dmaone/CSI/MagValve/Cortron_80-551101_rev_D.JPG

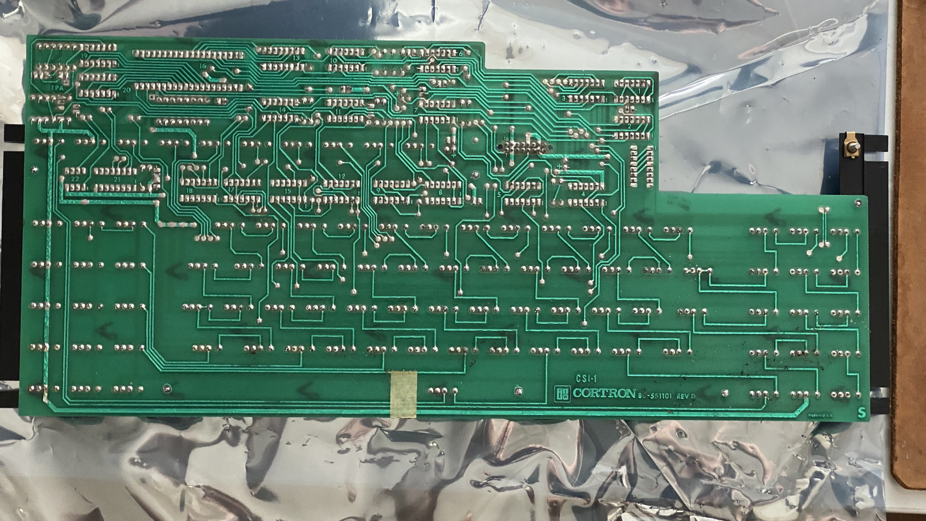
MagValve/Cortron_80-551101_rev_D.JPG
