dmaone/CSI/MagValve/Waveforms/Cortron/Oscillograms/Agilent diffprobe/Screen_2019-10-03000012.png

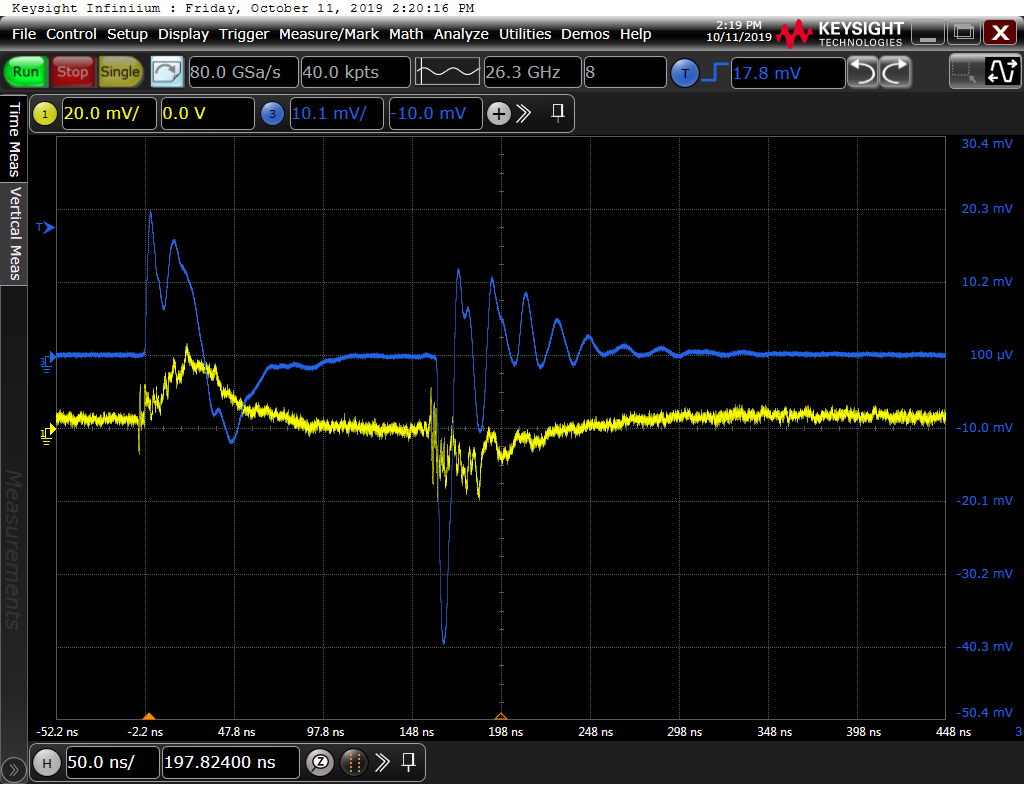
MagValve/Waveforms/Cortron/Oscillograms/Agilent diffprobe/Screen_2019-10-03000012.png
