dmaone/CSI/MagValve/Waveforms/Cortron/Oscillograms/ctrlr-side_ground_bounce/Tek000.png

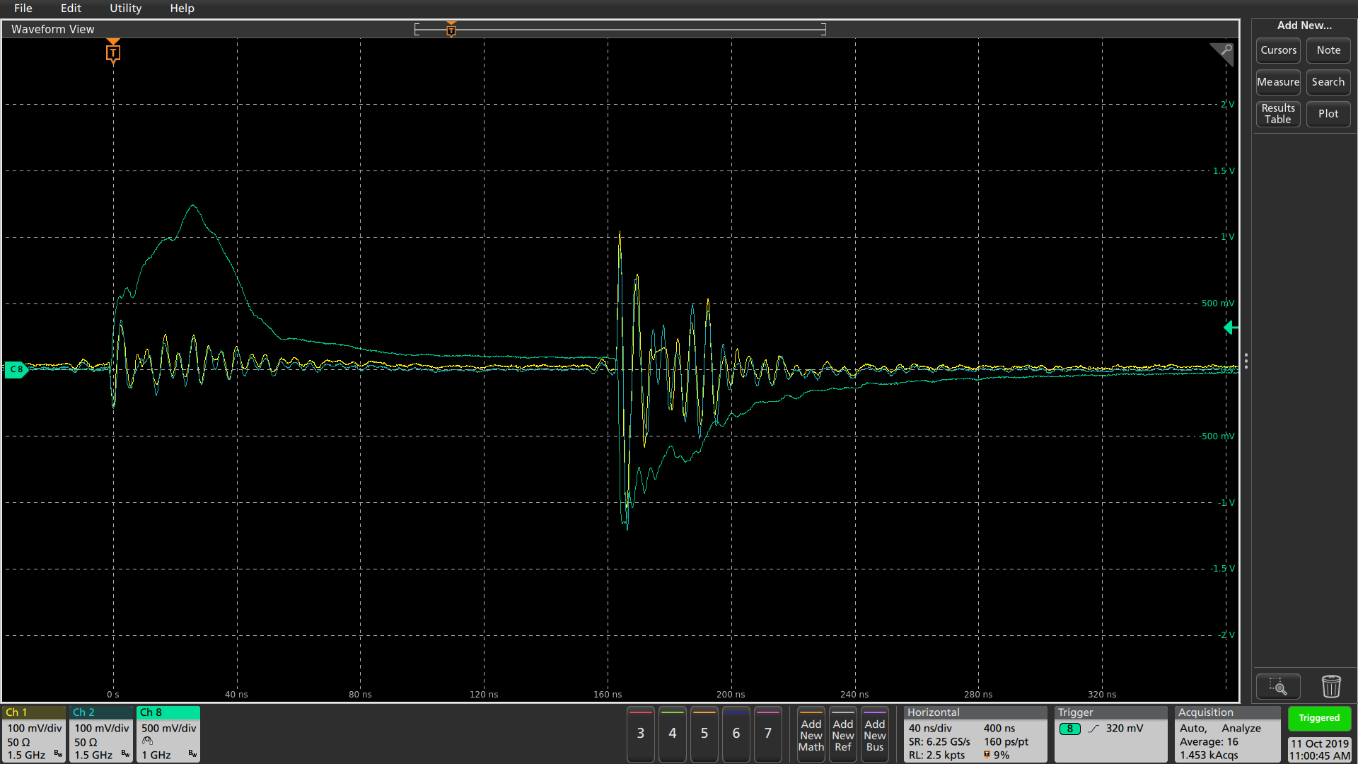
MagValve/Waveforms/Cortron/Oscillograms/ctrlr-side_ground_bounce/Tek000.png
