dmaone/CSI/MagValve/Waveforms/Cortron/Oscillograms/drive_ground_bounce_per_channel/Tek001_003.png

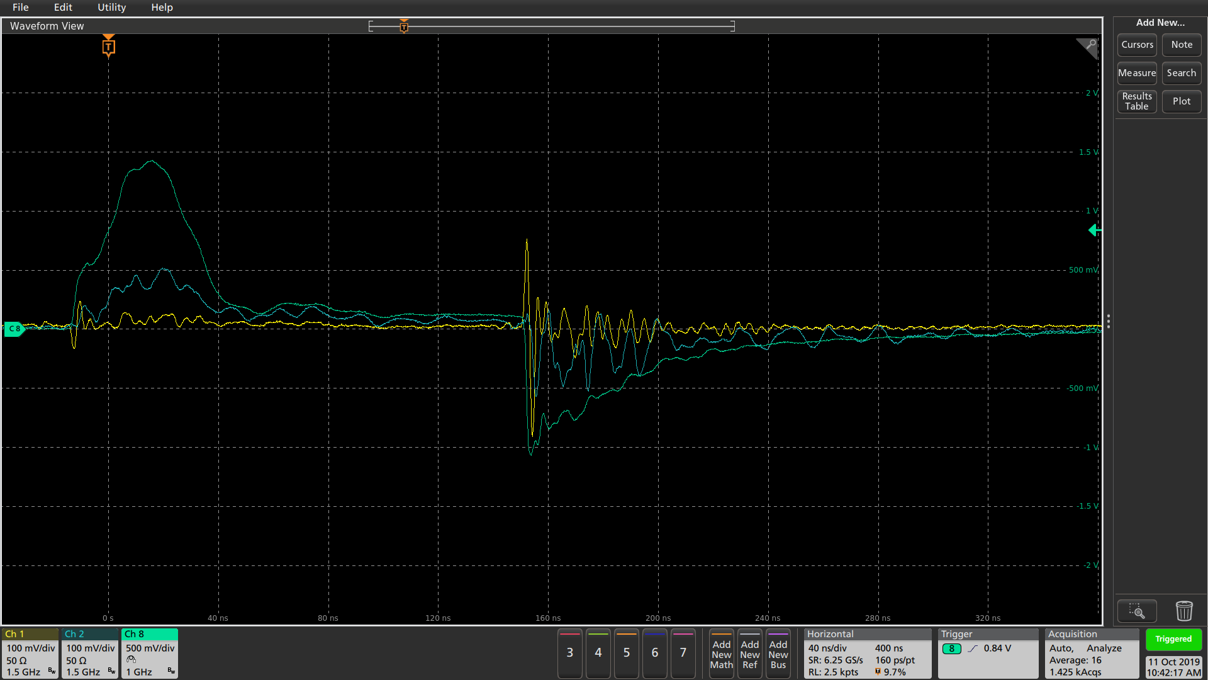
MagValve/Waveforms/Cortron/Oscillograms/drive_ground_bounce_per_channel/Tek001_003.png
