dmaone/CSI/MagValve/Waveforms/Cortron/Oscillograms/Latency/Tek001_002.png

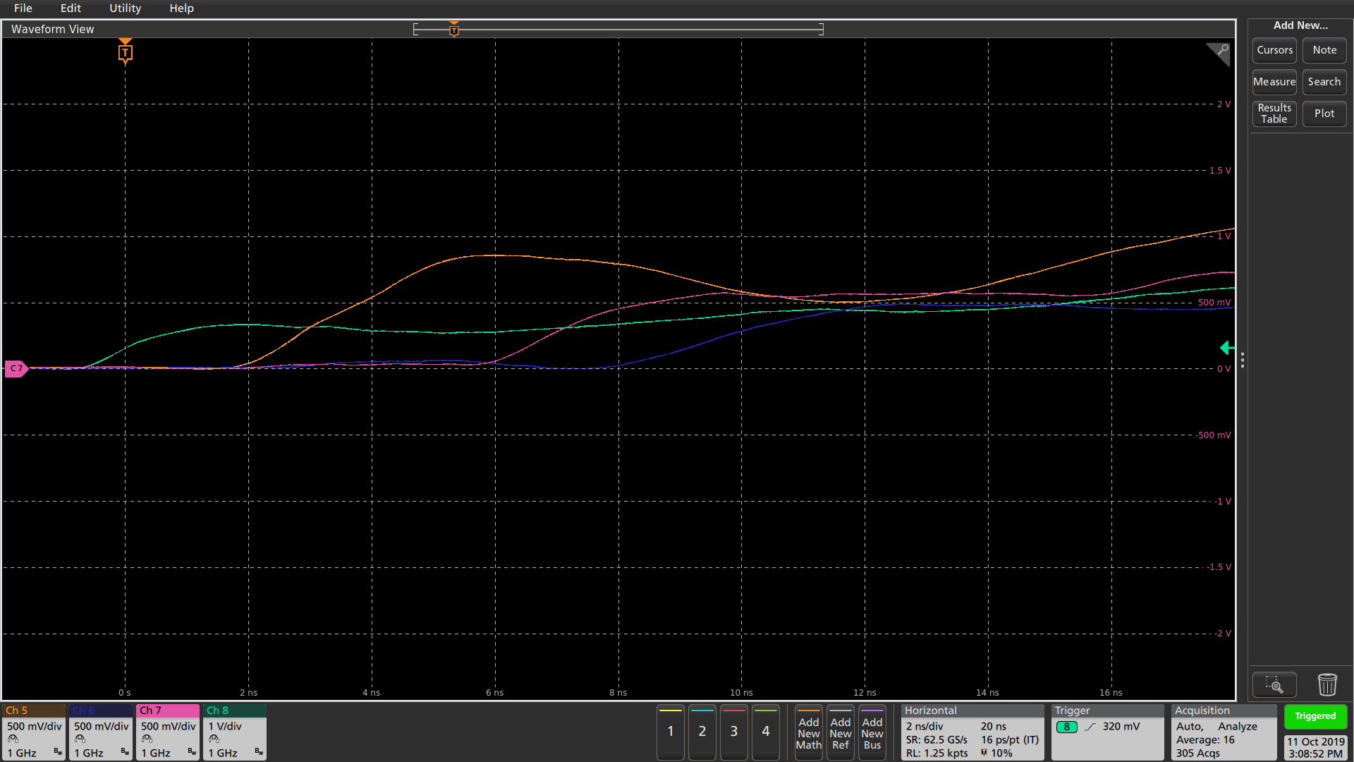
MagValve/Waveforms/Cortron/Oscillograms/Latency/Tek001_002.png
