dmaone/CSI/MagValve/Waveforms/Cortron/Oscillograms/Latency/Tek001_006.png

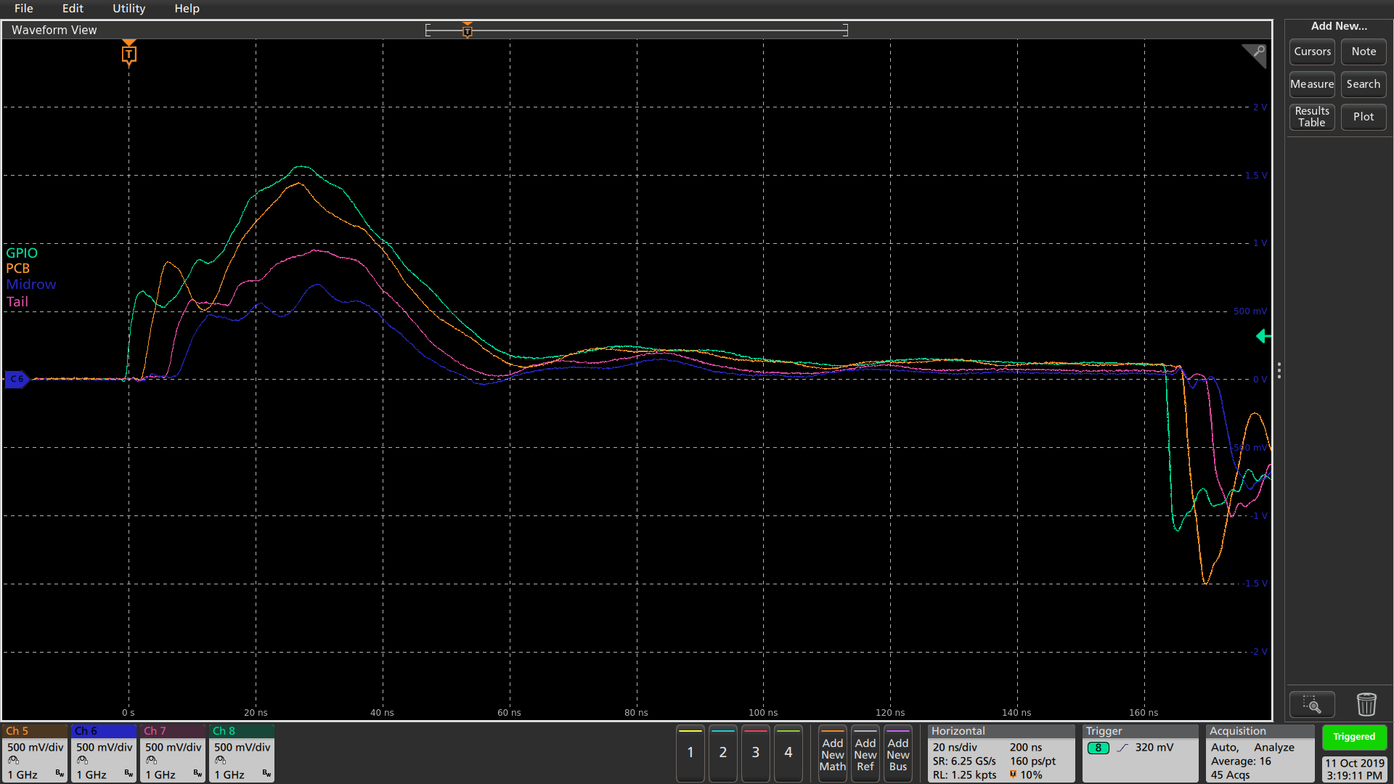
MagValve/Waveforms/Cortron/Oscillograms/Latency/Tek001_006.png
