dmaone/CSI/MagValve/Waveforms/Cortron/Oscillograms/Latency/Tek001_007.png

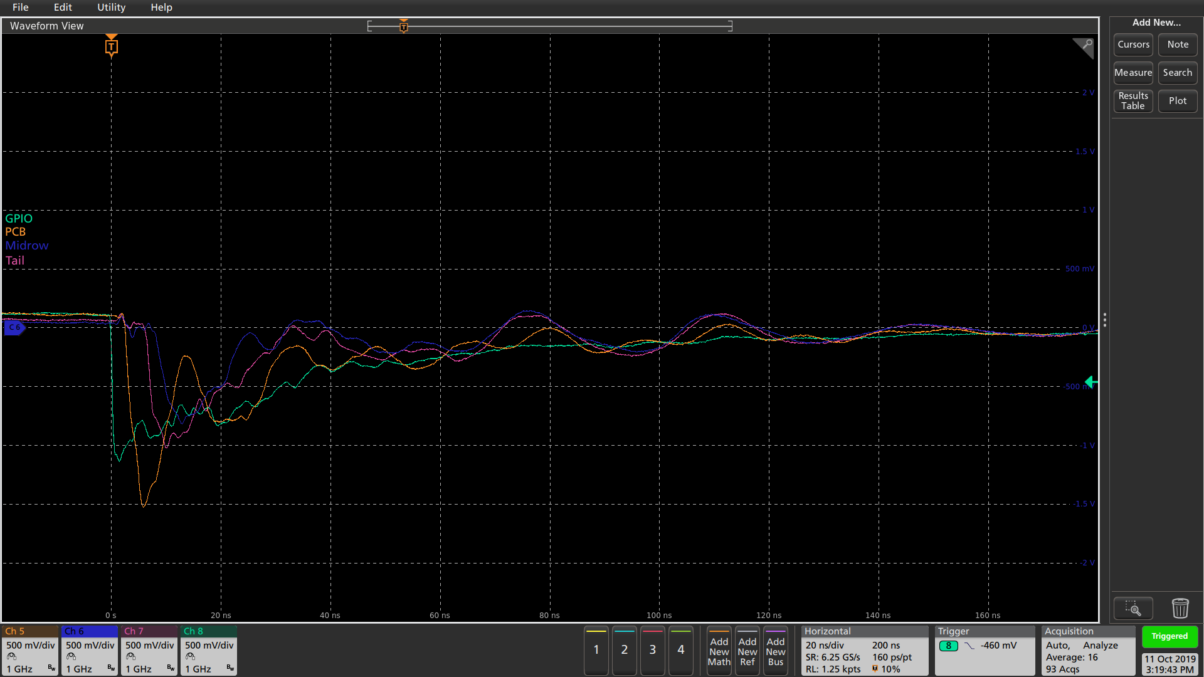
MagValve/Waveforms/Cortron/Oscillograms/Latency/Tek001_007.png
