dmaone/CSI/MagValve/Waveforms/Cortron/Oscillograms/Latency/Tek001_008.png

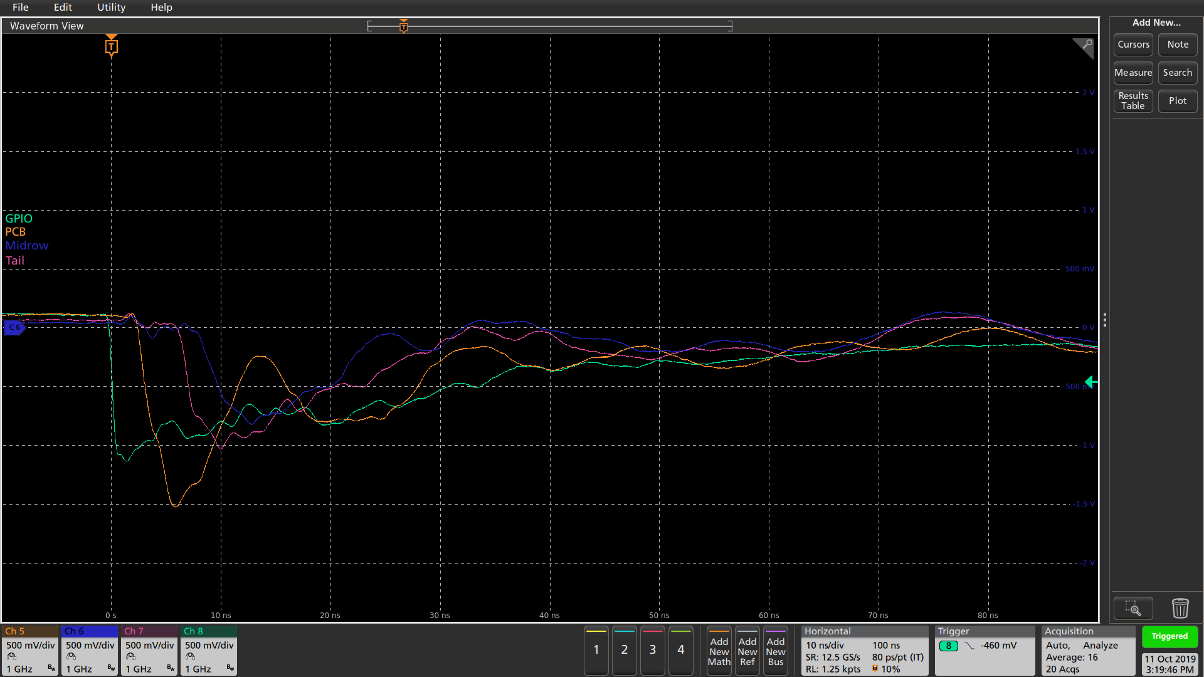
MagValve/Waveforms/Cortron/Oscillograms/Latency/Tek001_008.png
