dmaone/CSI/MagValve/Waveforms/Cortron/Oscillograms/loss_in_pcb/Tek001_010.png

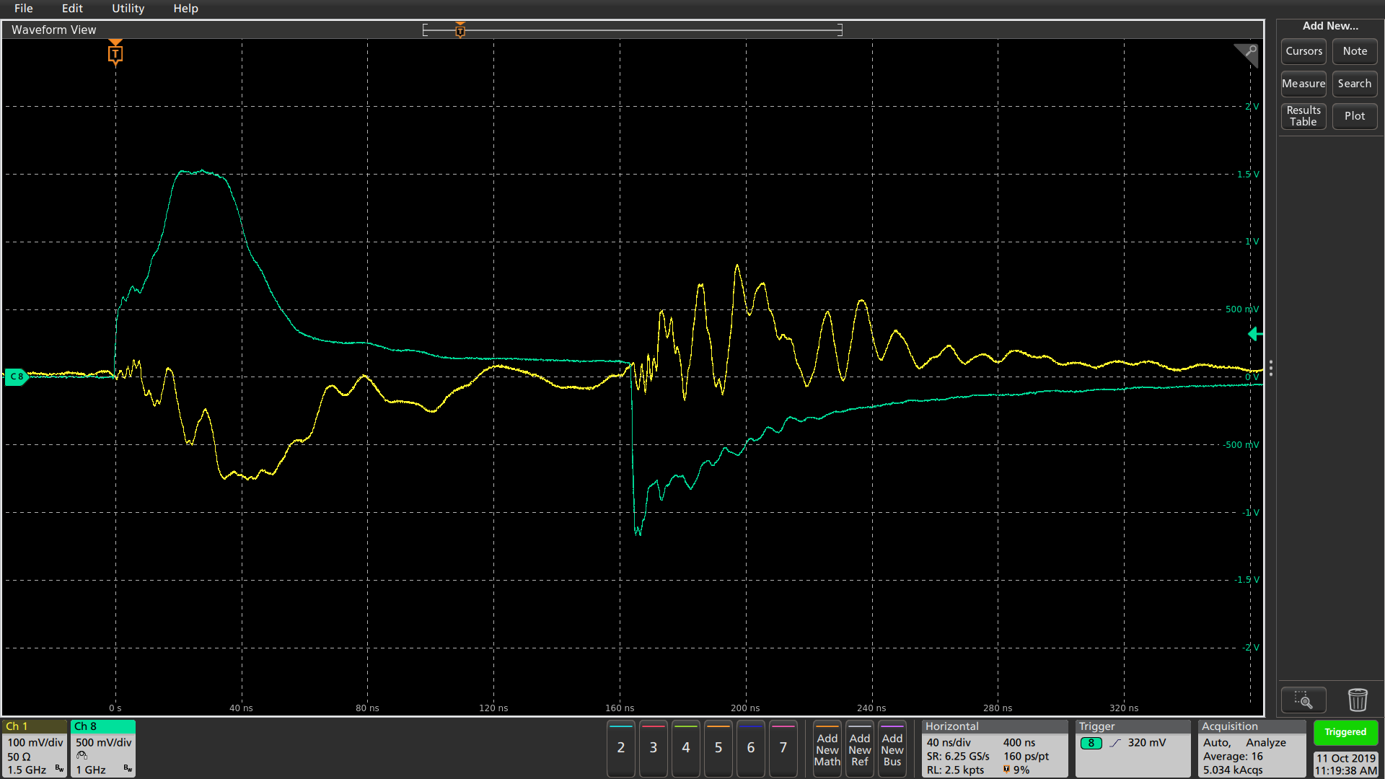
MagValve/Waveforms/Cortron/Oscillograms/loss_in_pcb/Tek001_010.png
