dmaone/CSI/MagValve/Waveforms/Cortron/Oscillograms/loss_in_sense_gnd/Tek001_001.png

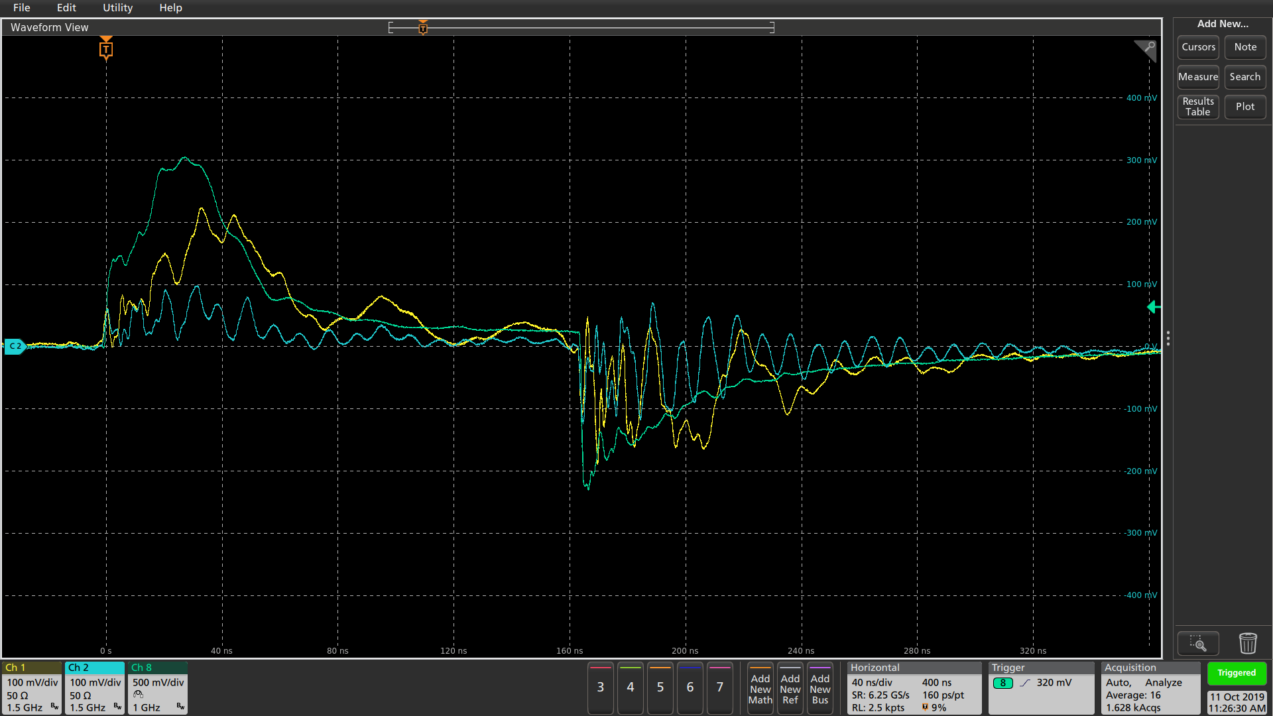
MagValve/Waveforms/Cortron/Oscillograms/loss_in_sense_gnd/Tek001_001.png
