dmaone/CSI/MagValve/Waveforms/Cortron/Oscillograms/mid_row_column_sense/All_channels_pressed.png

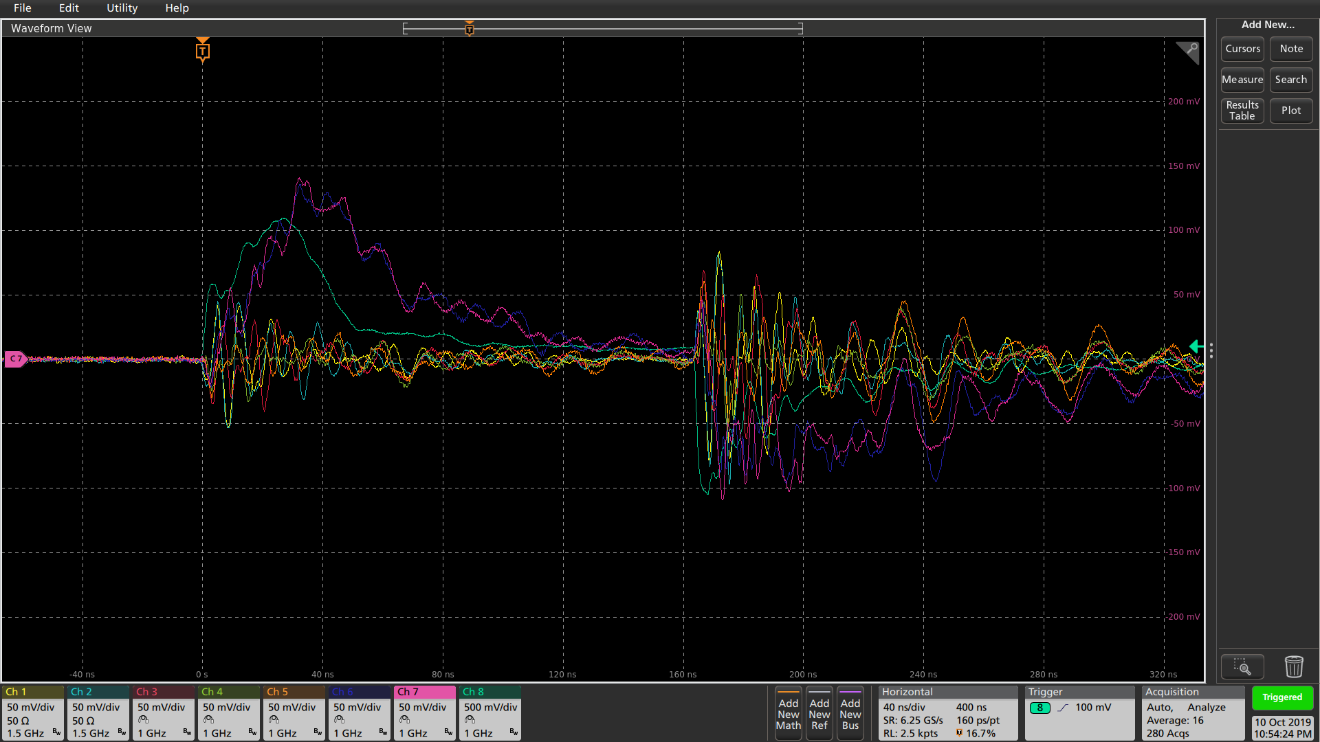
MagValve/Waveforms/Cortron/Oscillograms/mid_row_column_sense/All_channels_pressed.png
