dmaone/CSI/MagValve/Waveforms/Cortron/Oscillograms/mid_row_column_sense/r3_pressed.png

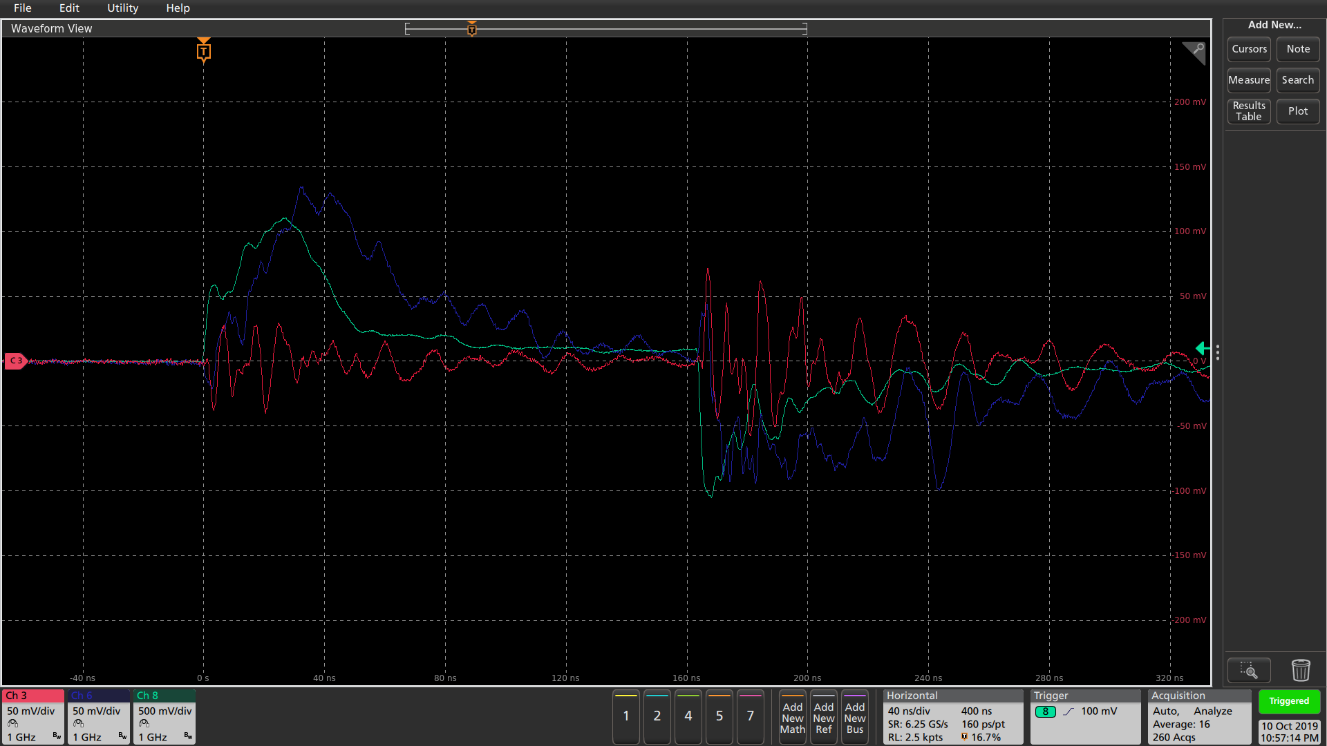
MagValve/Waveforms/Cortron/Oscillograms/mid_row_column_sense/r3_pressed.png
