dmaone/CSI/MagValve/Waveforms/Cortron/Oscillograms/row direct drive fast pcb gnd/Tek001_012.png

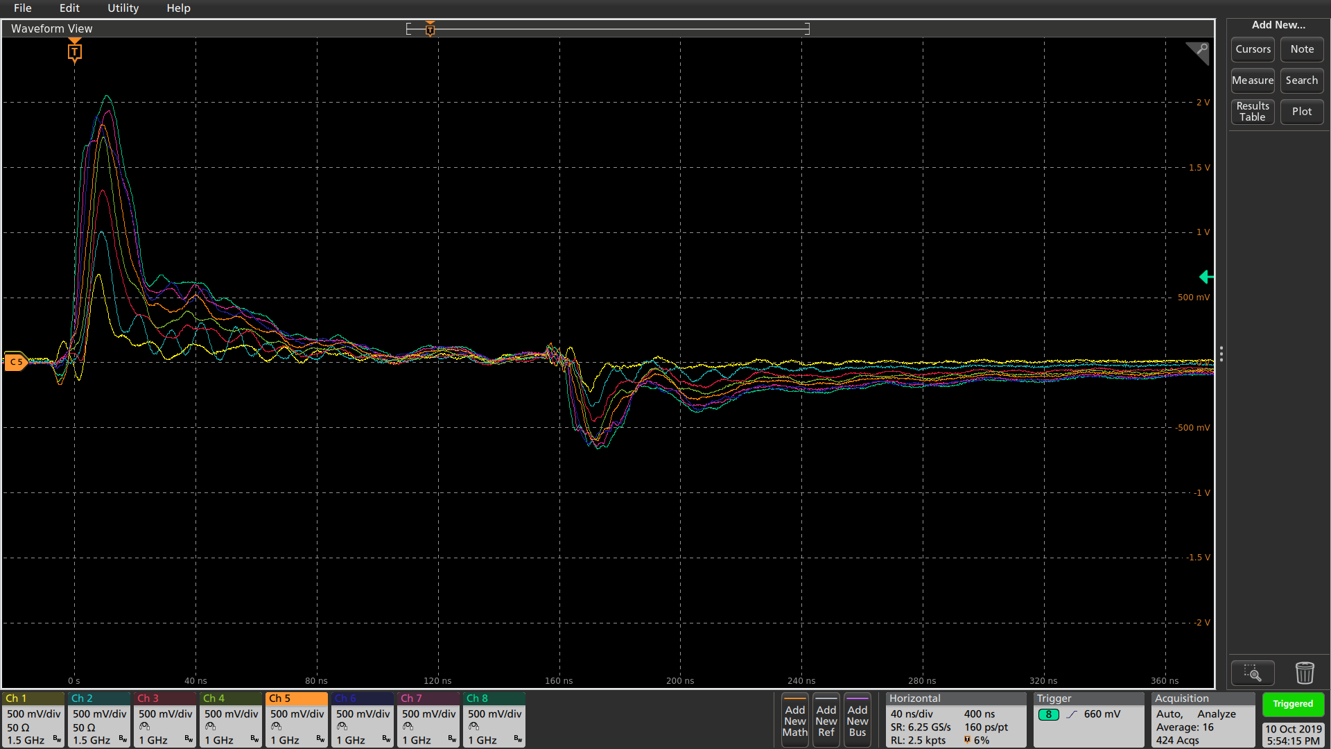
MagValve/Waveforms/Cortron/Oscillograms/row direct drive fast pcb gnd/Tek001_012.png
