dmaone/CSI/MagValve/Waveforms/Cortron/Oscillograms/row direct drive fast pcb gnd/Tek001_014.png

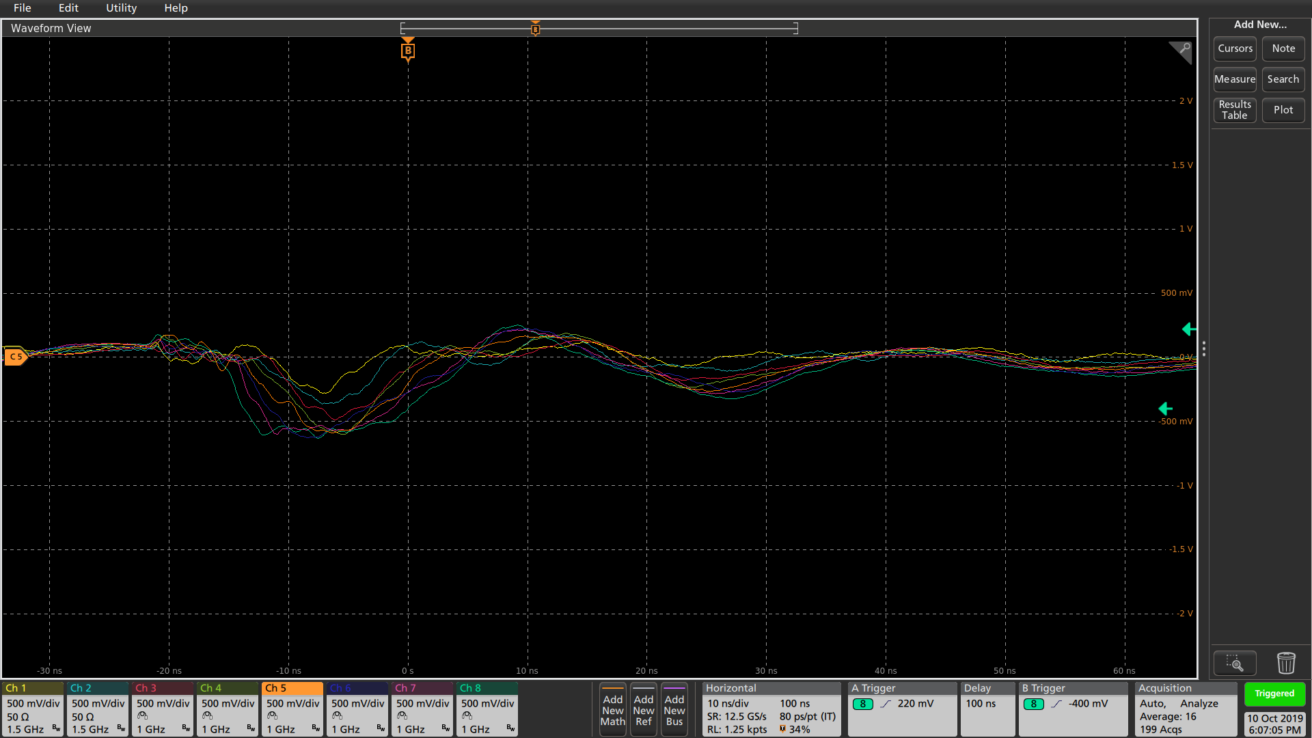
MagValve/Waveforms/Cortron/Oscillograms/row direct drive fast pcb gnd/Tek001_014.png
