dmaone/CSI/MagValve/Waveforms/Cortron/Oscillograms/row direct drive pcb gnd/Tek001_018.png

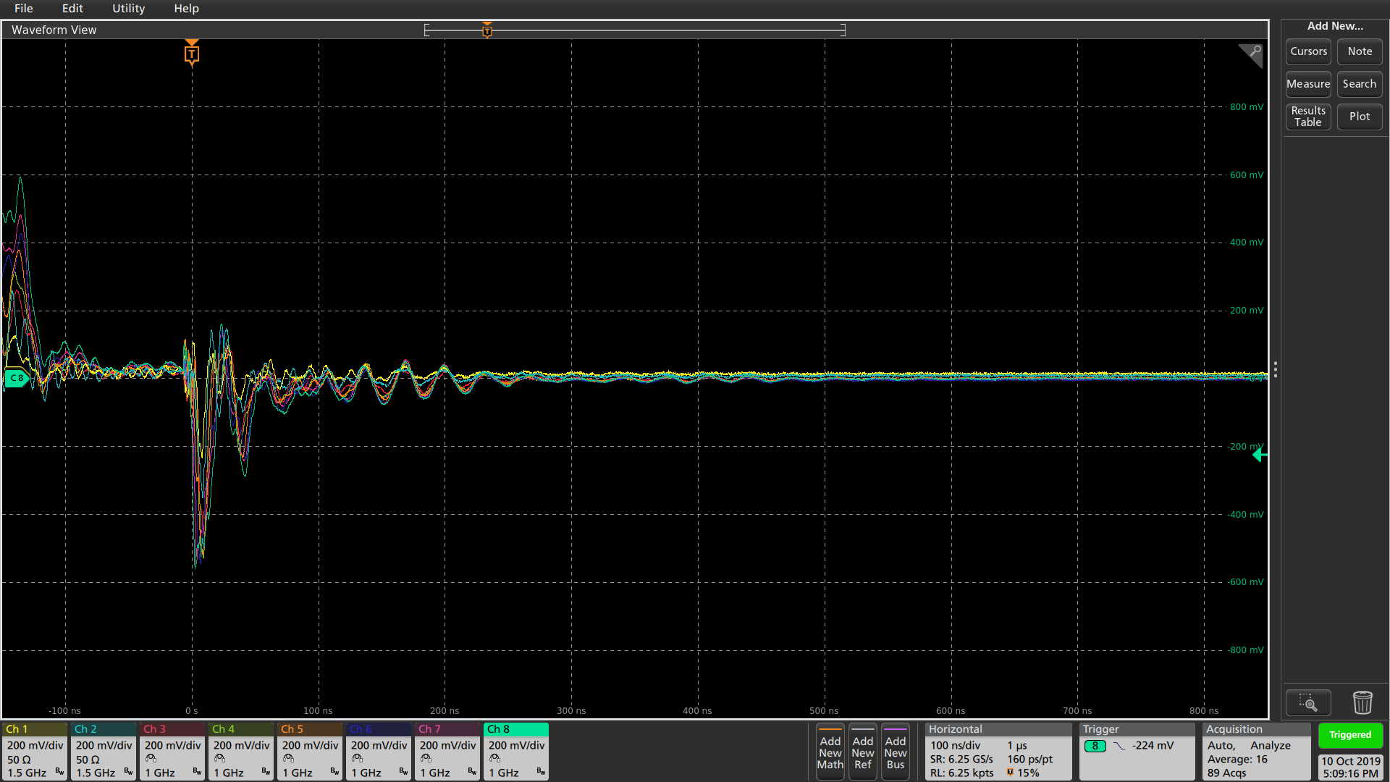
MagValve/Waveforms/Cortron/Oscillograms/row direct drive pcb gnd/Tek001_018.png
