dmaone/CSI/MagValve/Waveforms/Cortron/Oscillograms/row direct drive pcb gnd/Tek001_019.png

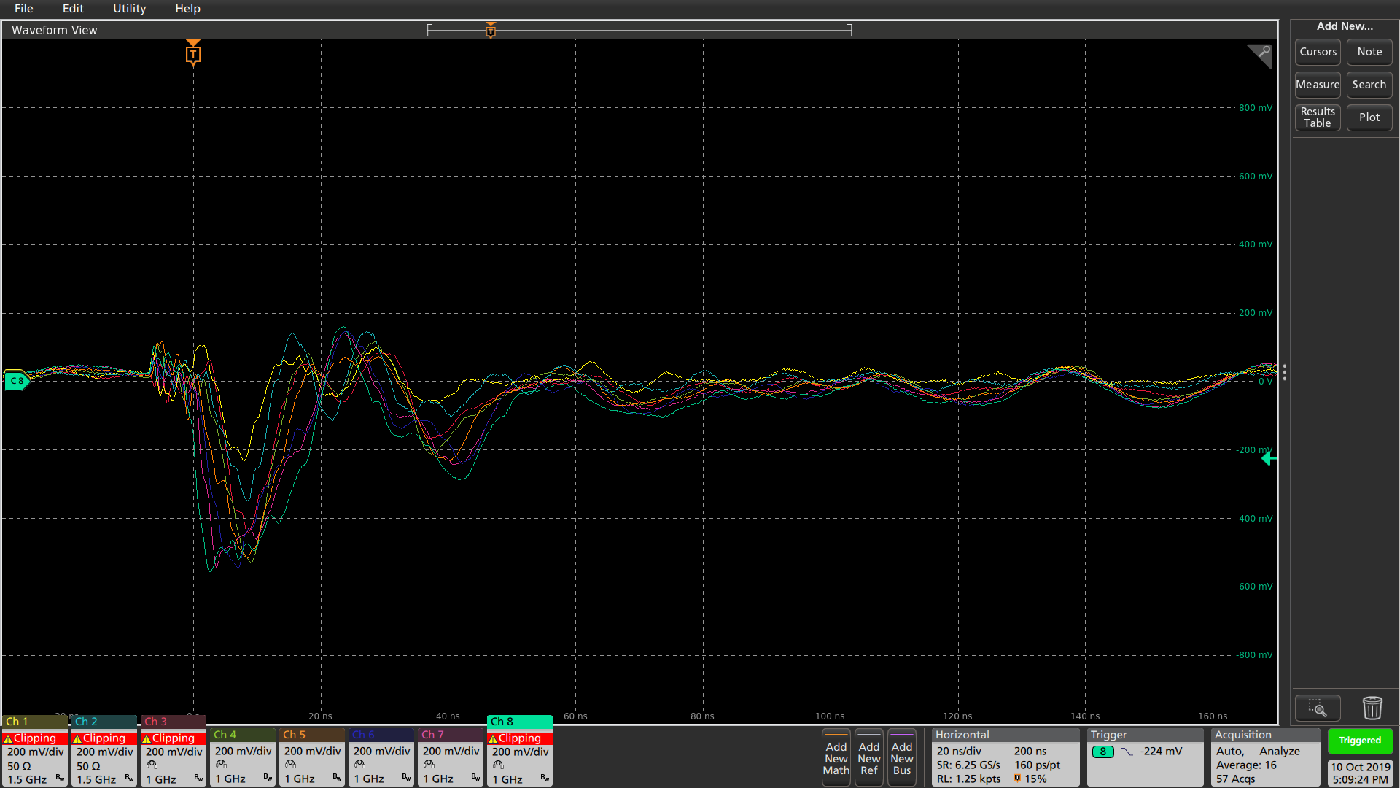
MagValve/Waveforms/Cortron/Oscillograms/row direct drive pcb gnd/Tek001_019.png
