dmaone/CSI/MagValve/Waveforms/Cortron/Oscillograms/row direct drive pcb gnd/Tek001_020.png

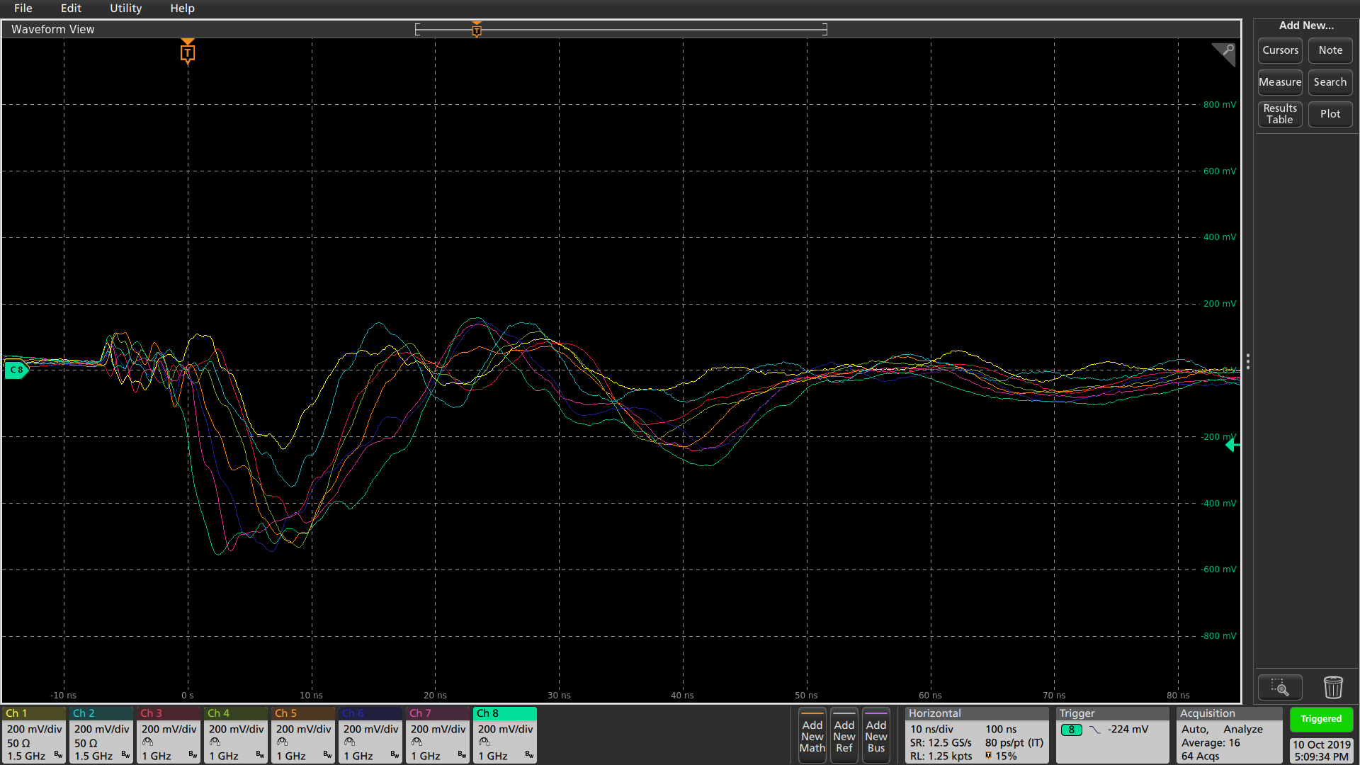
MagValve/Waveforms/Cortron/Oscillograms/row direct drive pcb gnd/Tek001_020.png
