dmaone/CSI/MagValve/Waveforms/Cortron/Oscillograms/row sense side fast vs slow/Tek001_009.png

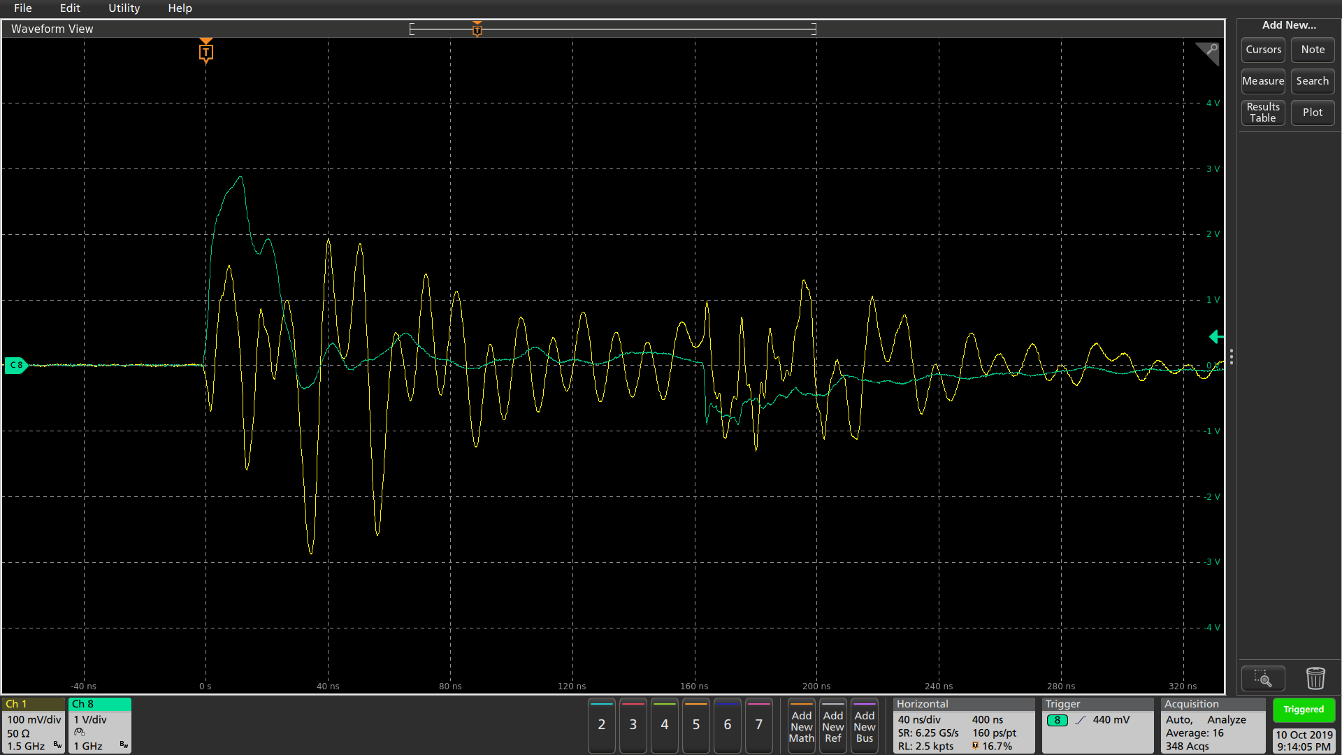
MagValve/Waveforms/Cortron/Oscillograms/row sense side fast vs slow/Tek001_009.png
