dmaone/CSI/MagValve/Waveforms/Cortron/Oscillograms/row sense side fast vs slow/Tek001_011.png

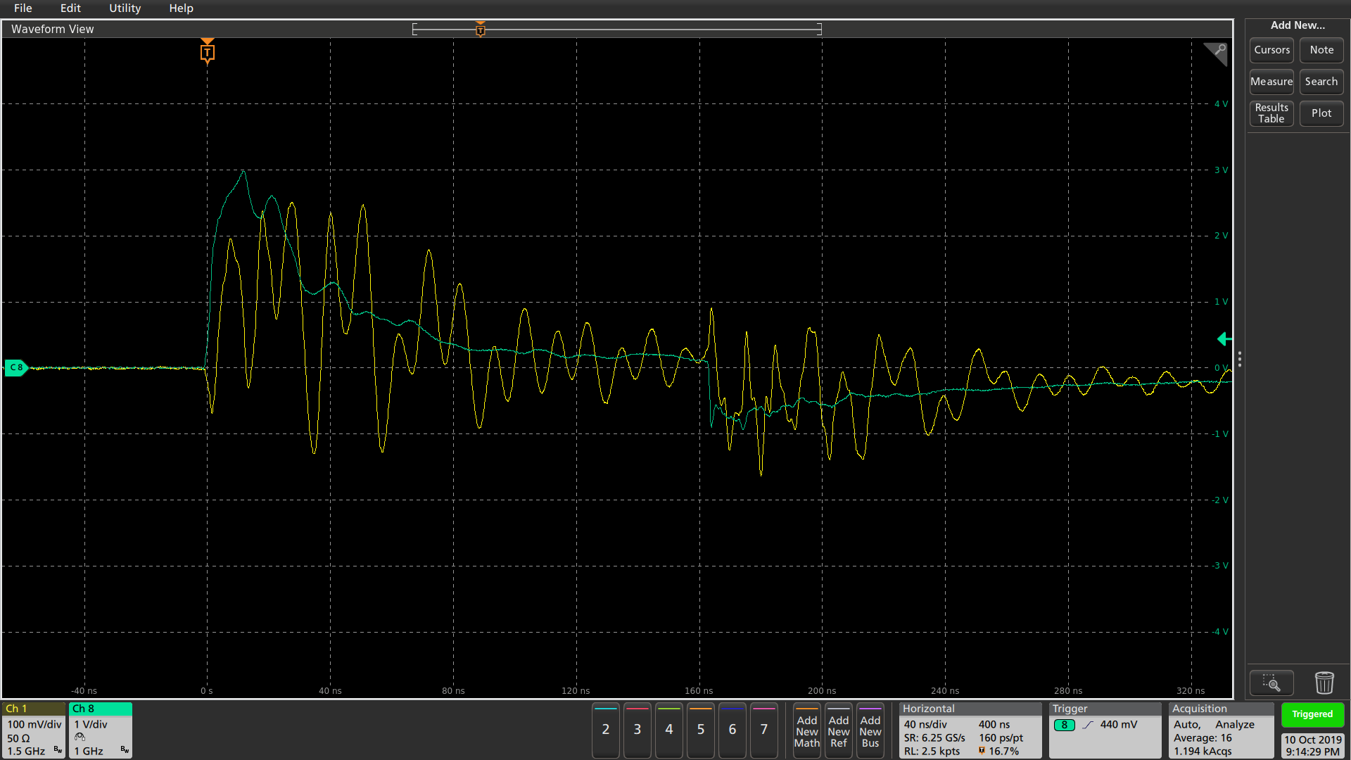
MagValve/Waveforms/Cortron/Oscillograms/row sense side fast vs slow/Tek001_011.png
