dmaone/CSI/MagValve/Waveforms/Cortron/Oscillograms/row sense side fast vs slow/Tek001_014.png

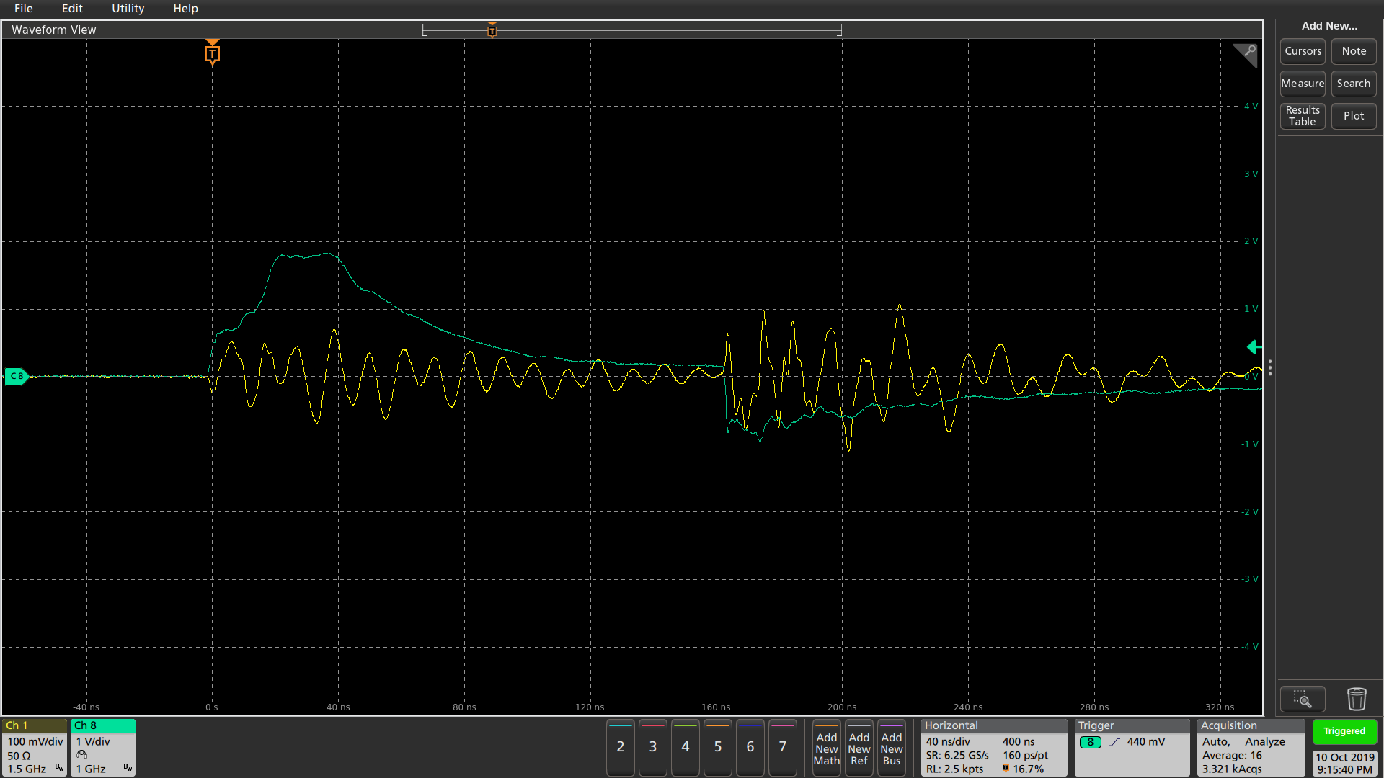
MagValve/Waveforms/Cortron/Oscillograms/row sense side fast vs slow/Tek001_014.png
