dmaone/CSI/MagValve/Waveforms/Cortron/Oscillograms/row_dd_fast_r2_pcbgnd/Tek001_002.png

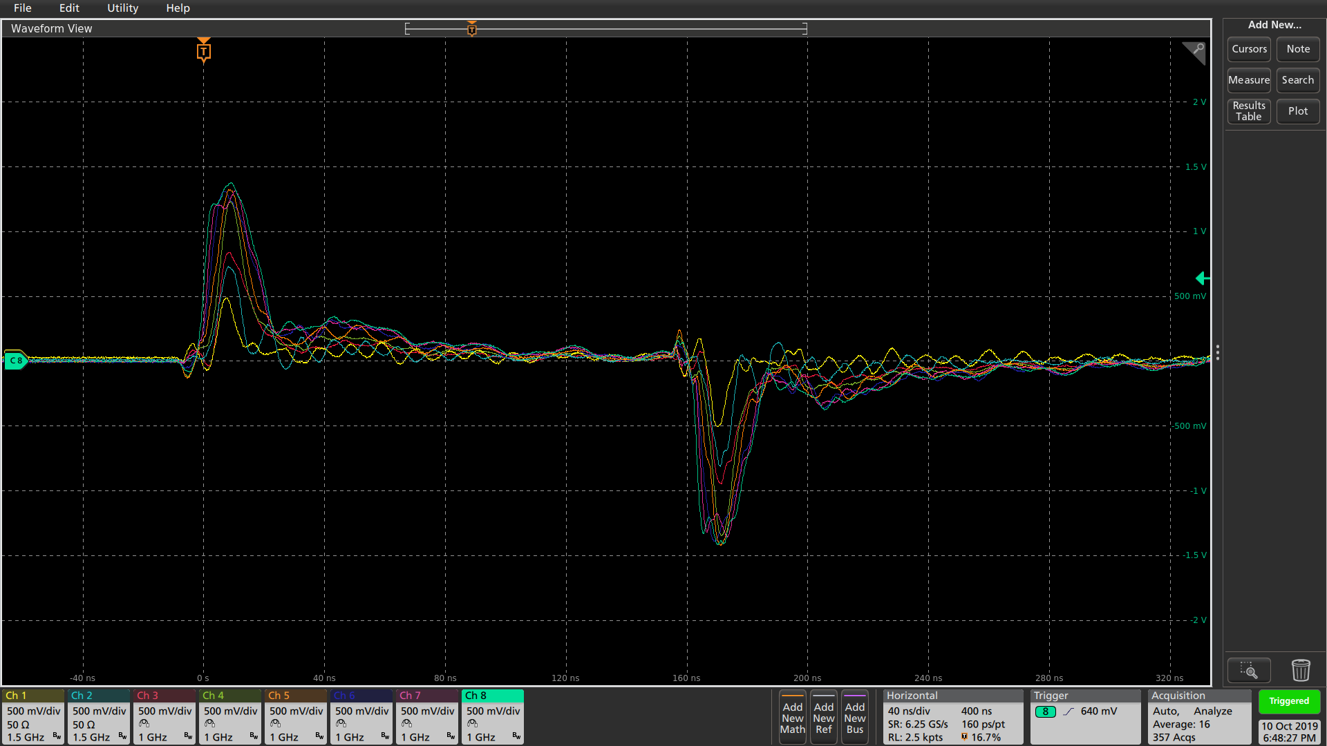
MagValve/Waveforms/Cortron/Oscillograms/row_dd_fast_r2_pcbgnd/Tek001_002.png
