dmaone/CSI/MagValve/Waveforms/Cortron/Oscillograms/row_dd_r1_pcbgnd/Tek001_002.png

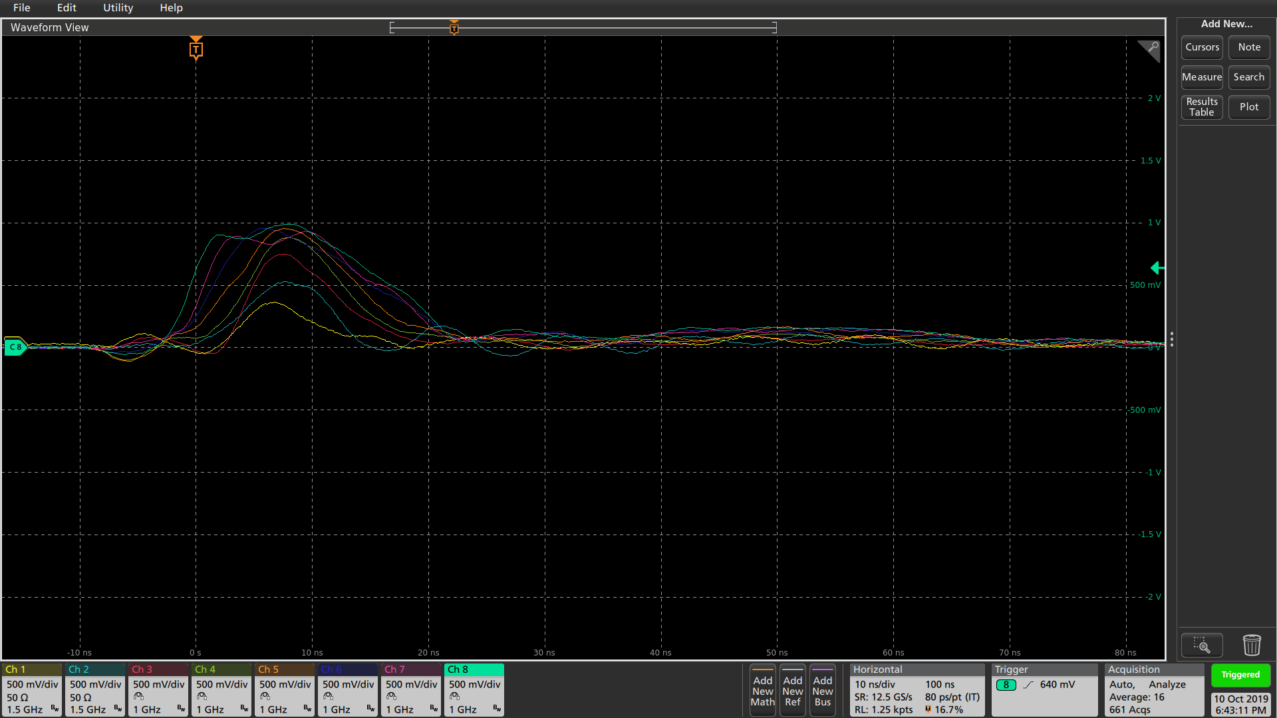
MagValve/Waveforms/Cortron/Oscillograms/row_dd_r1_pcbgnd/Tek001_002.png
