dmaone/CSI/MagValve/Waveforms/Cortron/Oscillograms/row_sense_200r_fastslow_ctrlr/Tek001_001.png

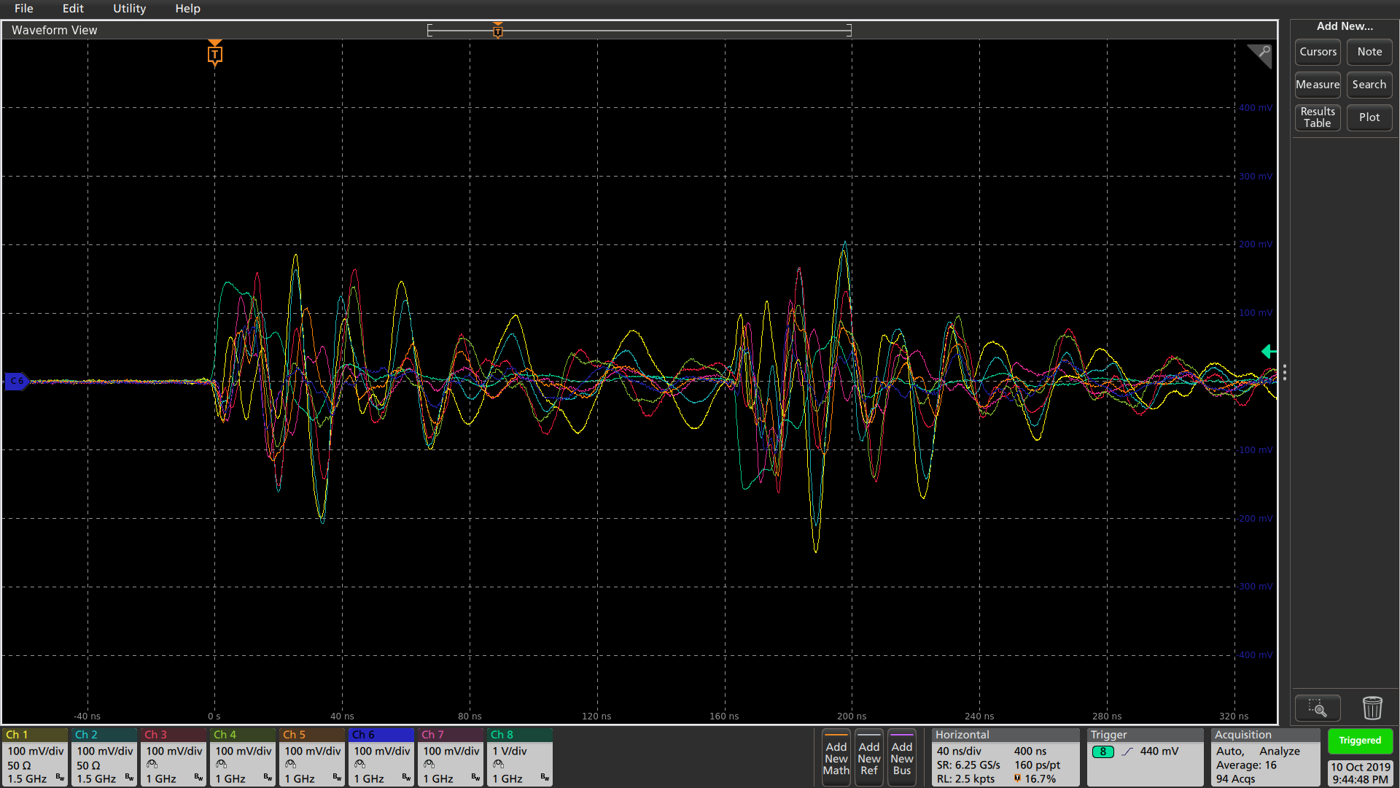
MagValve/Waveforms/Cortron/Oscillograms/row_sense_200r_fastslow_ctrlr/Tek001_001.png
