dmaone/CSI/MagValve/Waveforms/Cortron/Oscillograms/row_sense_200r_fastslow_ctrlr/Tek001_020.png

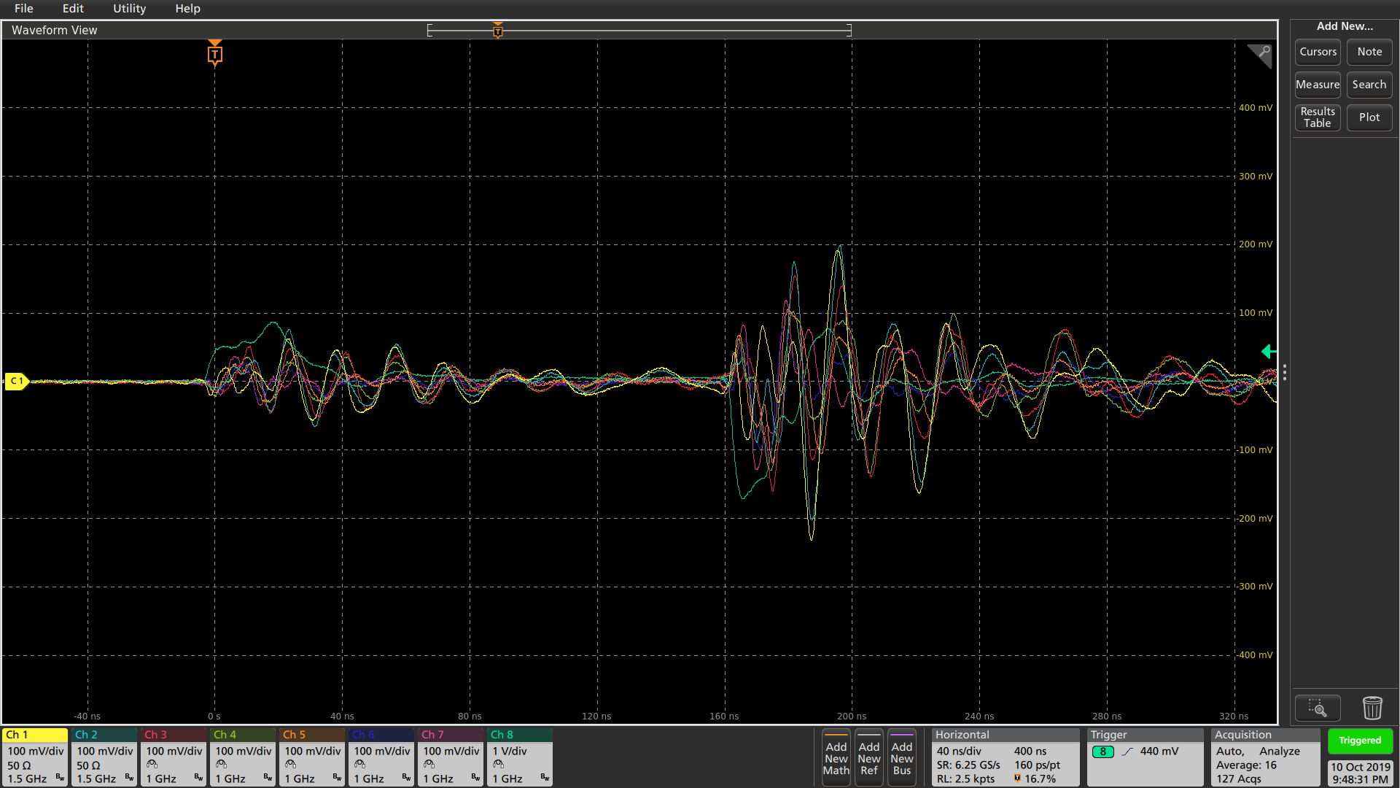
MagValve/Waveforms/Cortron/Oscillograms/row_sense_200r_fastslow_ctrlr/Tek001_020.png
