dmaone/CSI/MagValve/Waveforms/Cortron/Oscillograms/row_sense_side_200r_fast_slow/Tek001_019.png

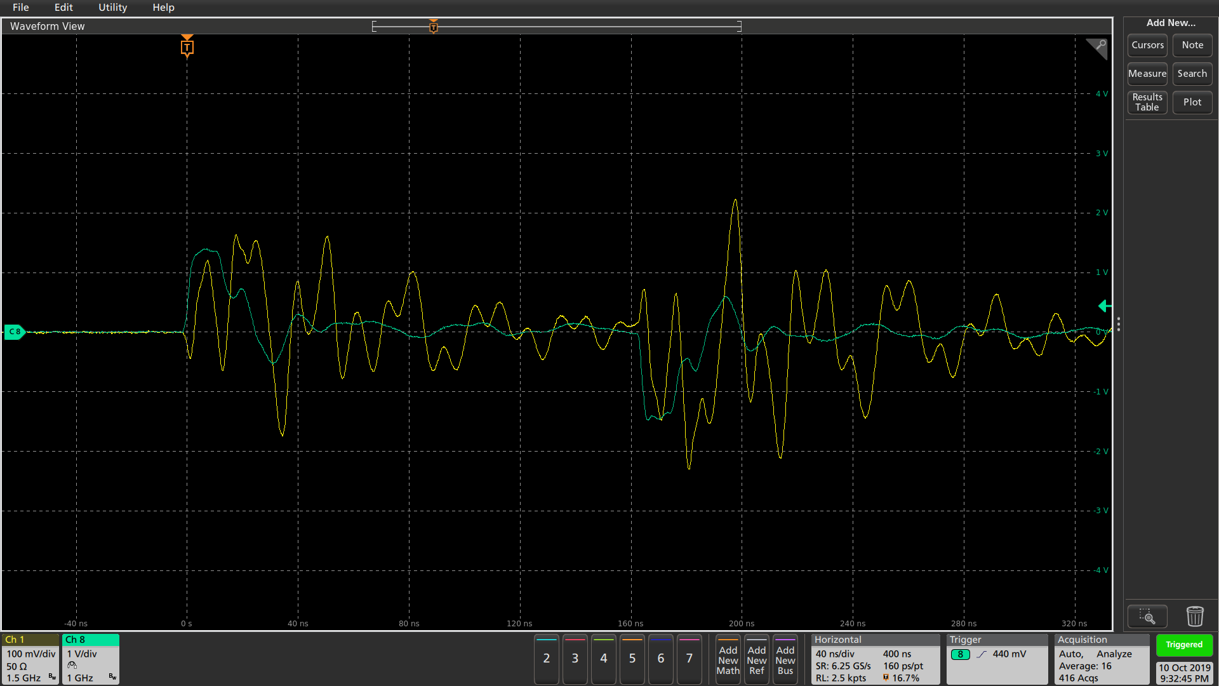
MagValve/Waveforms/Cortron/Oscillograms/row_sense_side_200r_fast_slow/Tek001_019.png
