dmaone/CSI/MagValve/Waveforms/Cortron/2_rows_ground_at_far_end/DS1Z_QuickPrint6.png

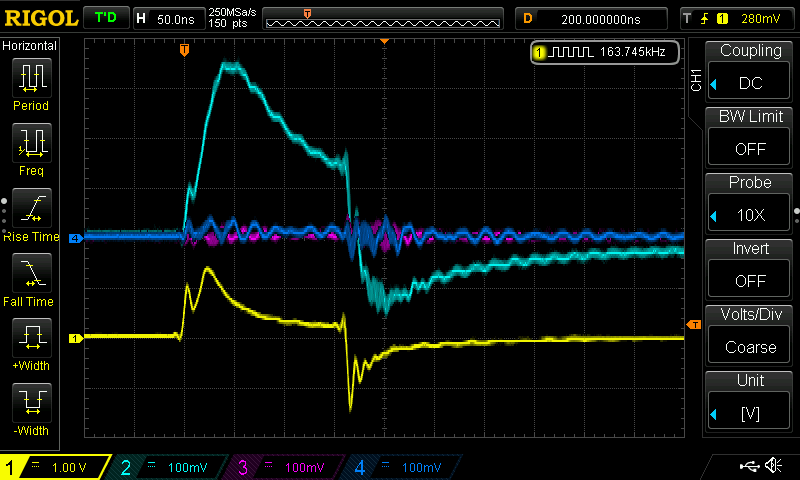
MagValve/Waveforms/Cortron/2_rows_ground_at_far_end/DS1Z_QuickPrint6.png
