dmaone/CSI/MagValve/Waveforms/Cortron/2_rows_trigger_inside_matrix_middle ground/DS1Z_QuickPrint6.png

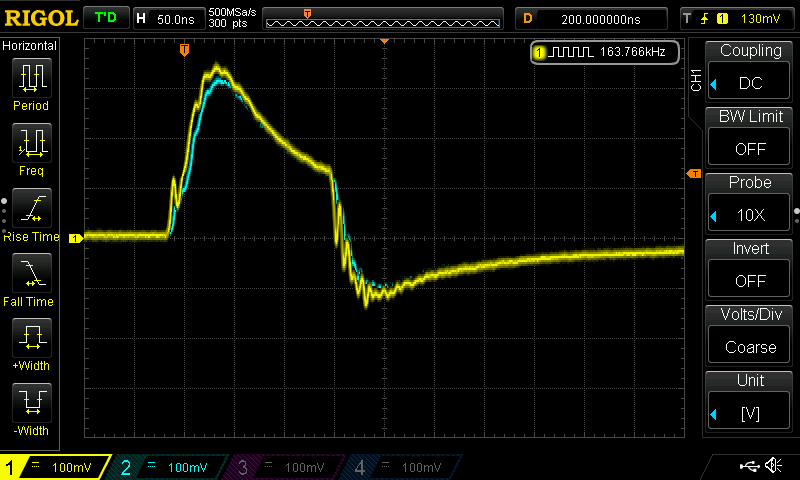
MagValve/Waveforms/Cortron/2_rows_trigger_inside_matrix_middle ground/DS1Z_QuickPrint6.png
