dmaone/CSI/MagValve/Waveforms/Cortron/2n_matrix/DS1Z_QuickPrint23.png

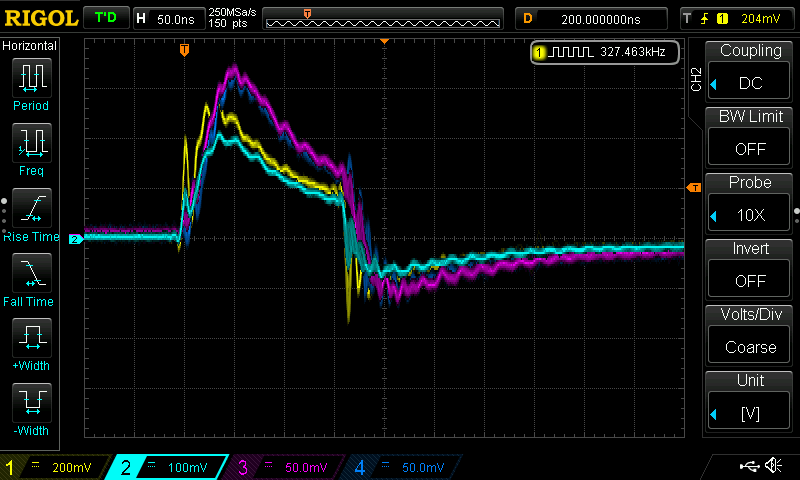
MagValve/Waveforms/Cortron/2n_matrix/DS1Z_QuickPrint23.png
