dmaone/CSI/MagValve/Waveforms/Cortron/2n_matrix/DS1Z_QuickPrint33.png

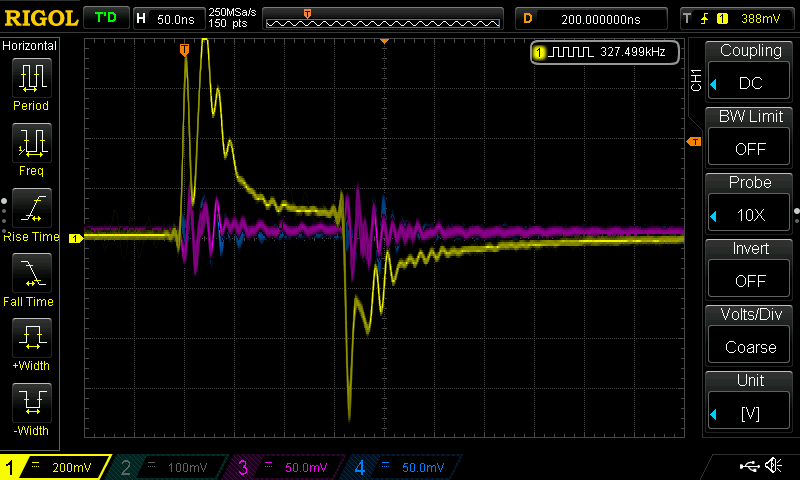
MagValve/Waveforms/Cortron/2n_matrix/DS1Z_QuickPrint33.png
