dmaone/CSI/MagValve/Waveforms/Cortron/5x4_columns/DS1Z_QuickPrint17.png

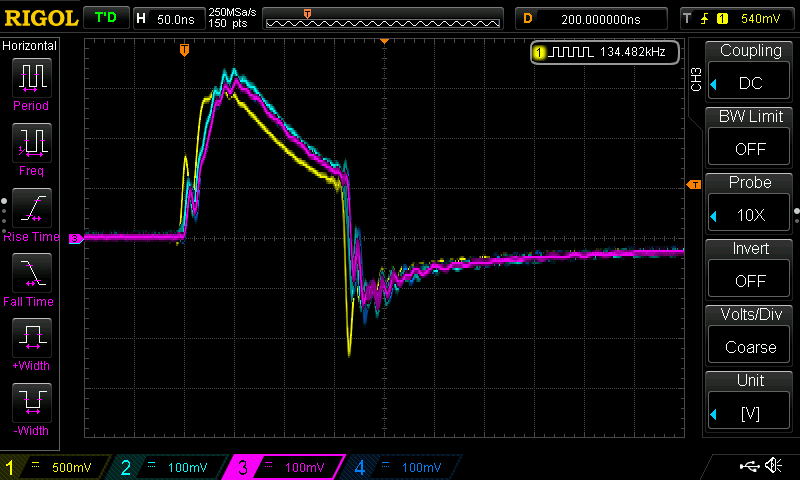
MagValve/Waveforms/Cortron/5x4_columns/DS1Z_QuickPrint17.png
