dmaone/CSI/MagValve/Waveforms/Cortron/5x4_rows/DS1Z_QuickPrint2.png

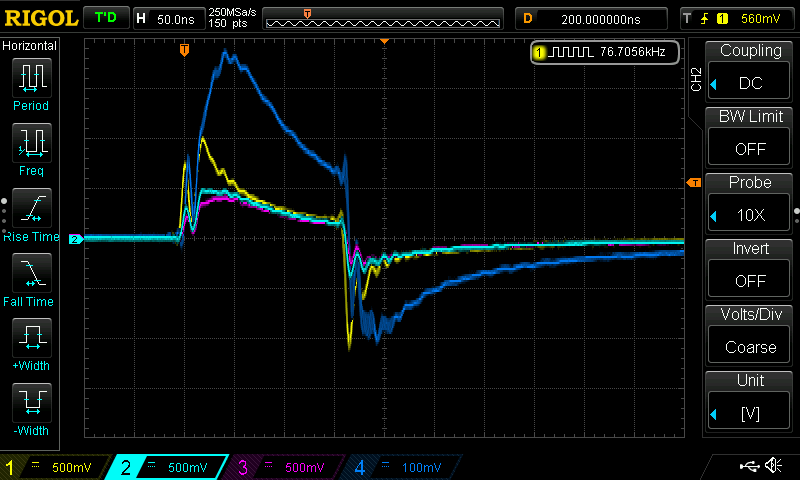
MagValve/Waveforms/Cortron/5x4_rows/DS1Z_QuickPrint2.png
