dmaone/CSI/MagValve/Waveforms/Cortron/5x4_shorted/DS1Z_QuickPrint4.png

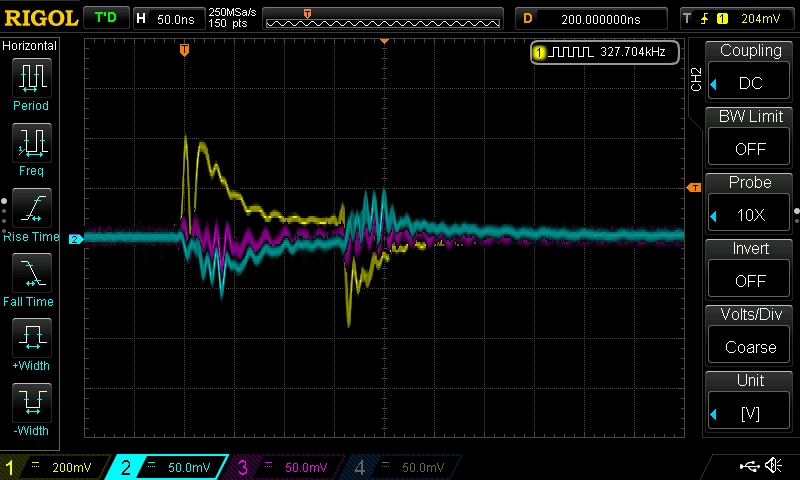
MagValve/Waveforms/Cortron/5x4_shorted/DS1Z_QuickPrint4.png
