dmaone/CSI/MagValve/Waveforms/Cortron/5x4_shorted/DS1Z_QuickPrint12.png

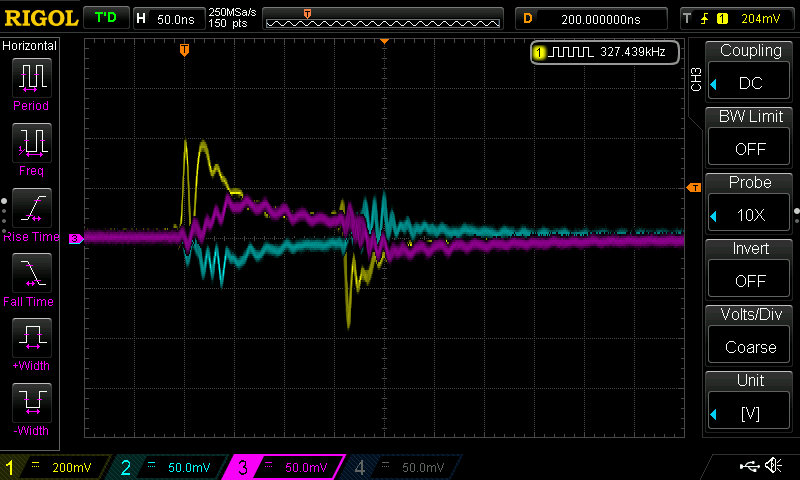
MagValve/Waveforms/Cortron/5x4_shorted/DS1Z_QuickPrint12.png
