dmaone/CSI/MagValve/Waveforms/Cortron/tall_grounded_chain/DS1Z_QuickPrint7.png

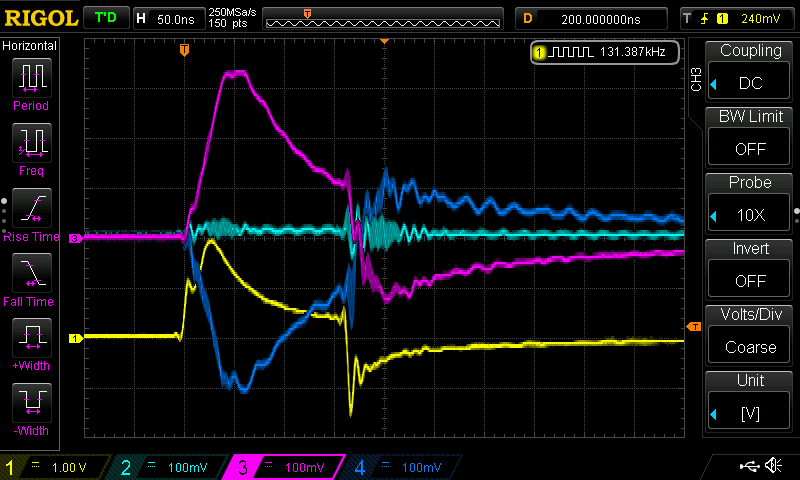
MagValve/Waveforms/Cortron/tall_grounded_chain/DS1Z_QuickPrint7.png
