dmaone/CSI/MagValve/Waveforms/Cortron/tall_grounded_chain/DS1Z_QuickPrint13.png

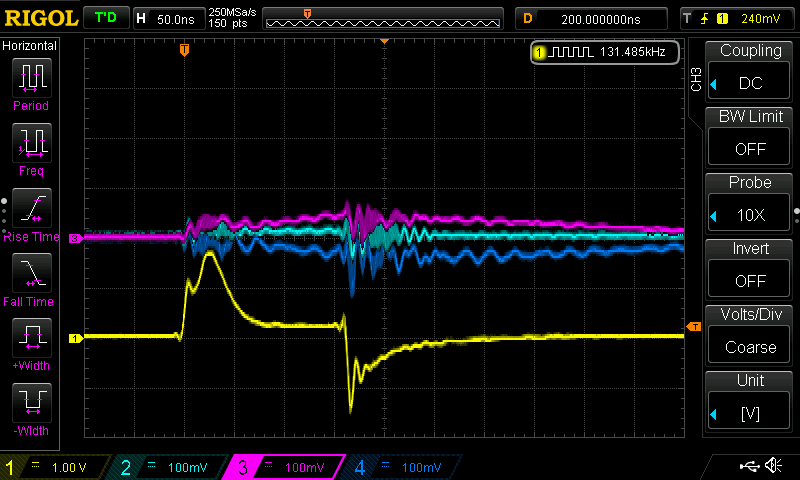
MagValve/Waveforms/Cortron/tall_grounded_chain/DS1Z_QuickPrint13.png
