dmaone/CSI/MagValve/Waveforms/Cortron/tall_single_chain/DS1Z_QuickPrint2.png

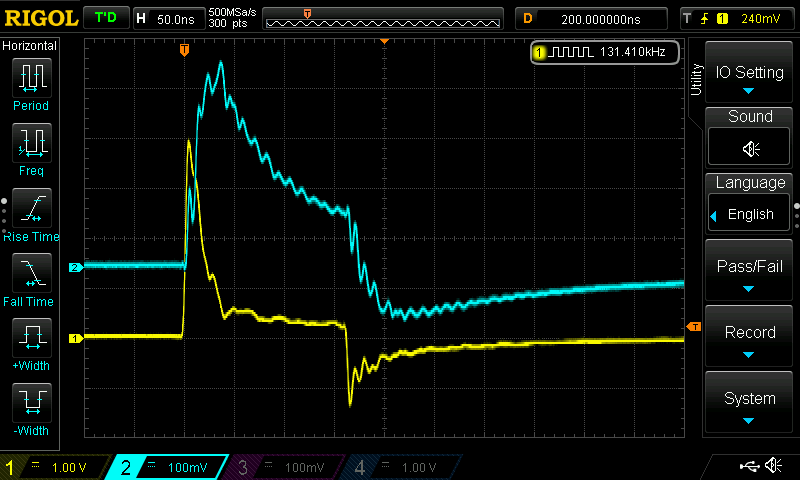
MagValve/Waveforms/Cortron/tall_single_chain/DS1Z_QuickPrint2.png
